Rastafouille/AirBee/CAD/boitier_solaire.SLDPRT

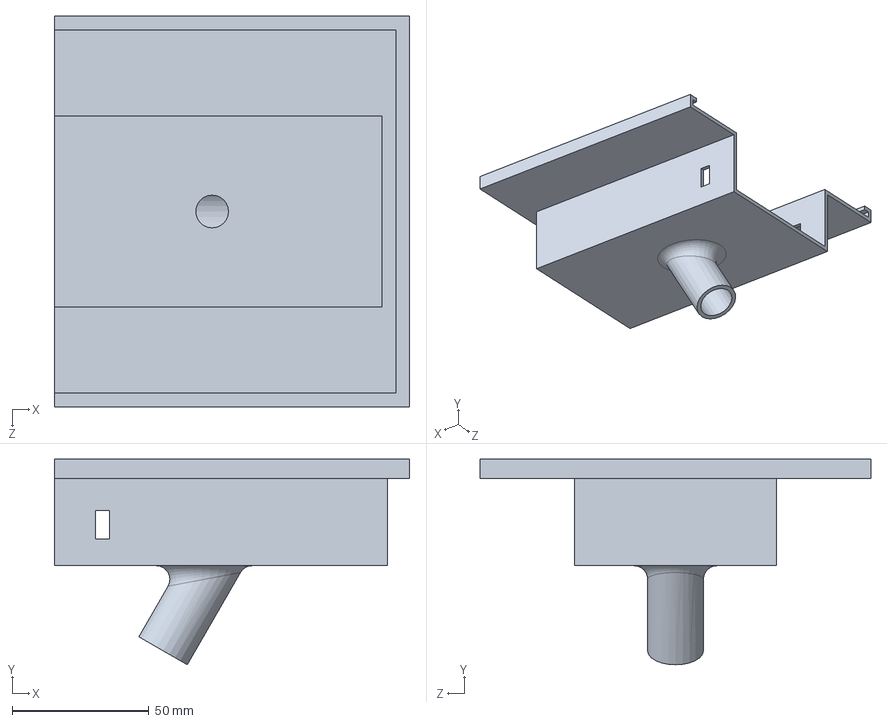
[picture p24: CAD file, 2017-10-08, an earlier design]
CAD/boitier_solaire.SLDPRT
130.0 x 75.3 x 143.0 mm
