Rastafouille/AirBee/CAD/boite_elect.SLDPRT

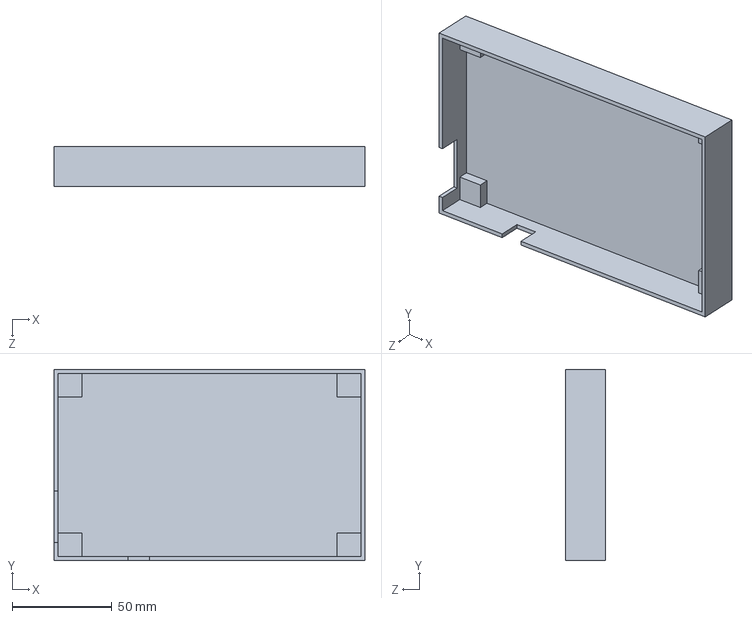
[picture p25: CAD file, 2017-10-08, an earlier design]
CAD/boite_elect.SLDPRT
156.0 x 96.0 x 20.0 mm
